BlueMustrad/AeroBrick/Images/All parts in Bambu Studio.png

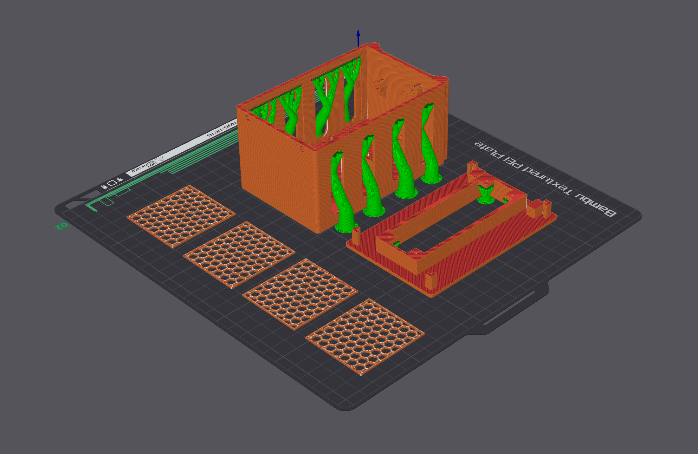
Images/All parts in Bambu Studio.png
