BlueMustrad/AeroBrick/Images/Full Main Assembly in Fusion.png

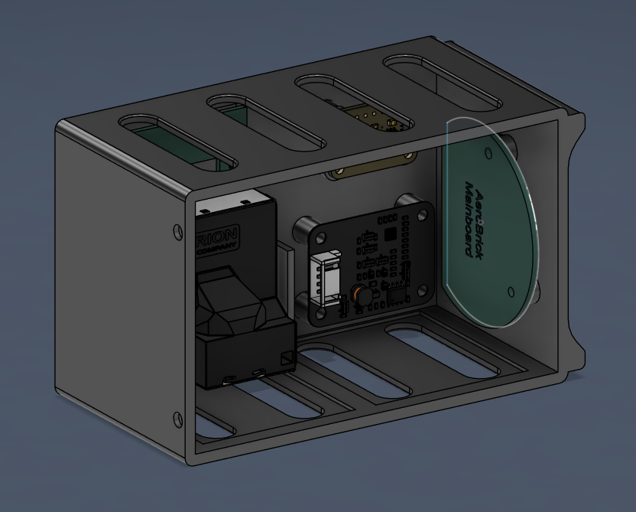
Images/Full Main Assembly in Fusion.png
