BlueMustrad/AeroBrick/Images/Full Top Assembly in Fusion.png

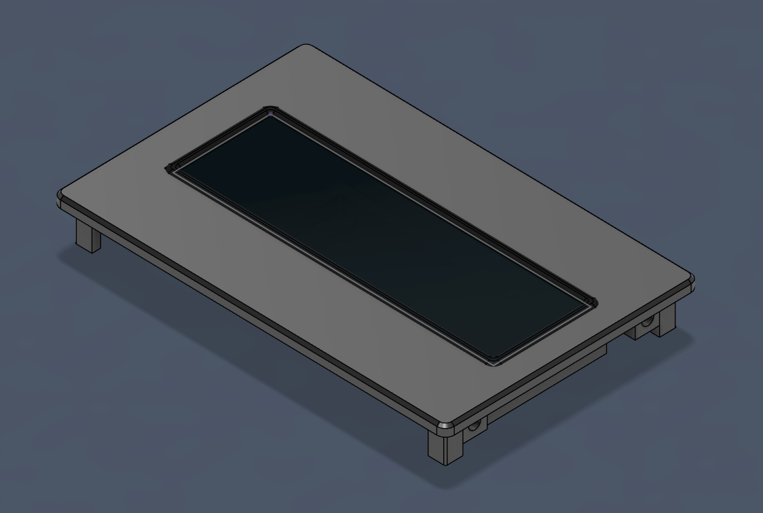
Images/Full Top Assembly in Fusion.png
